tinyvision-ai-inc/pico2-ice/Docs/images/20250409_100425.png

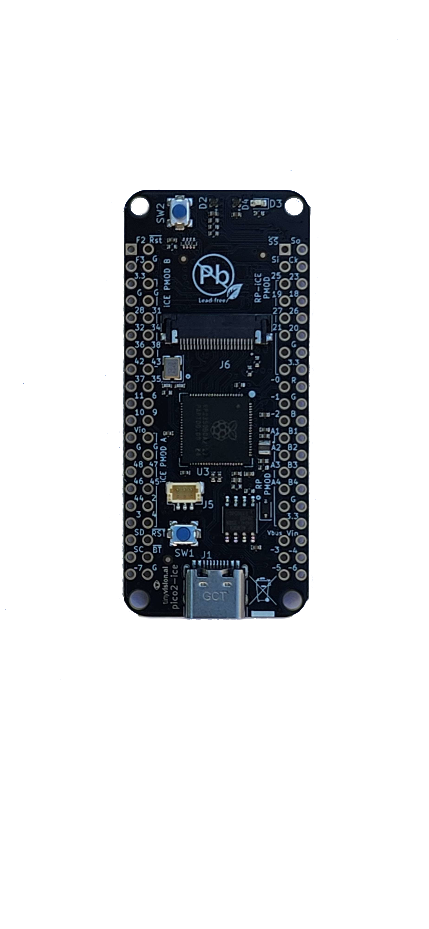
Docs/images/20250409_100425.png
